der-pw/HM-LC-SW1-BA-PCB_mini_MAX1724/Panel_2x4/Panel_2x4_Top.png

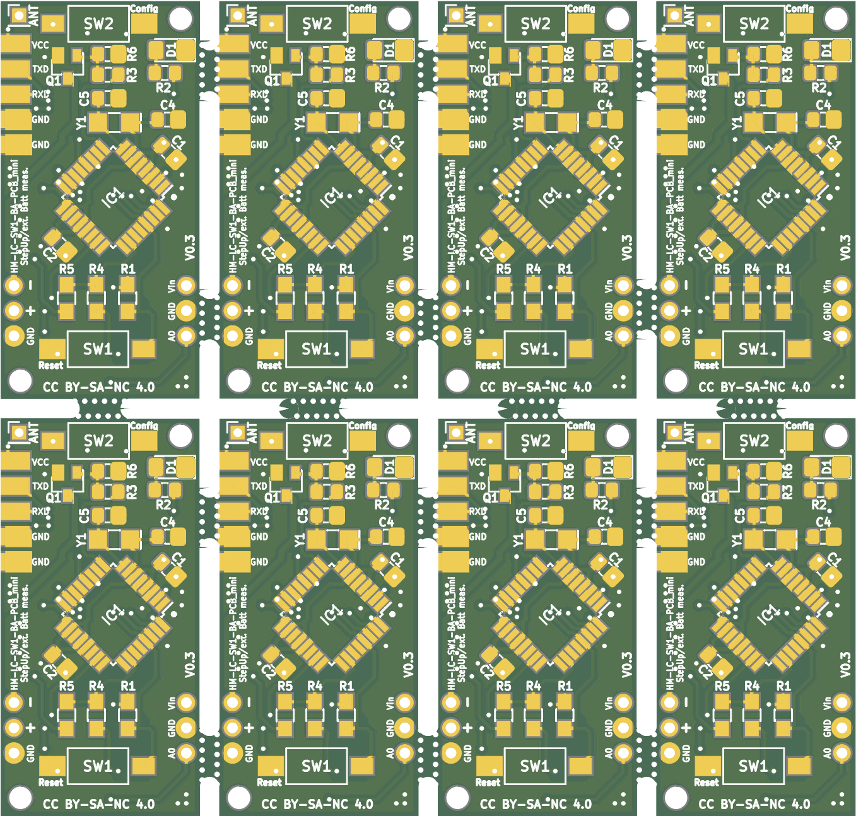
Panel_2x4/Panel_2x4_Top.png
